hnz1102/timeleapcam/code/src/autofocus.rs

use log::info;
use esp_camera_rs::CameraSensor;
use std::{thread, time::Duration};

#[allow(dead_code)]
const OV5640_RESET : u16 = 0x3000;
const OV5640_CHIPID_HIGH : u16 = 0x300a;
const OV5640_CHIPID_LOW : u16 = 0x300b;
const OV5640_CMD_MAIN : u16 = 0x3022;
const OV5640_CMD_ACK : u16 = 0x3023;
const OV5640_CMD_PARA0 : u16 = 0x3024;
const OV5640_CMD_PARA1 : u16 = 0x3025;
const OV5640_CMD_PARA2 : u16 = 0x3026;
const OV5640_CMD_PARA3 : u16 = 0x3027;
const OV5640_CMD_PARA4 : u16 = 0x3028;
const OV5640_CMD_FW_STATUS : u16 = 0x3029;
const AF_TRIG_SINGLE_AUTO_FOCUS : u8 = 0x03;
const AF_GET_FOCUS_RESULT : u8 = 0x07;
#[allow(dead_code)]
const AF_RELEASE_FOCUS : u8 = 0x08;
const AF_RELAUNCH_ZONE_CONFIGURATION : u8 = 0x12;
const AF_LAUNCH_DEFAULT_ZONE : u8 = 0x80;
const FW_STATUS_S_FIRMWARE : u8 = 0x7F;
#[allow(dead_code)]
const FW_STATUS_S_STARTUP : u8 = 0x7E;
const FW_STATUS_S_IDLE : u8 = 0x70;
#[allow(dead_code)]
const FW_STATUS_S_FOCUSED : u8 = 0x10;
#[allow(dead_code)]
const FW_STATUS_S_ZONE_CONFIG : u8 = 0x16;
#[allow(dead_code)]
const FW_STATUS_S_FOCUSING : u8 = 0x00; //0x00 - 0X0F, 0x80 - 0X8F
const ALL_MASK : u8 = 0xFF;

pub struct AutoFocus<'a> {
    sensor: &'a CameraSensor<'a>,
	enable: bool,
}

impl<'a> AutoFocus<'a> {
    pub fn new(sensor: &'a CameraSensor) -> Self {
        Self { sensor: sensor, enable: false }
    }

    pub fn init(&mut self) {
        let pidh = self.sensor.get_reg(OV5640_CHIPID_HIGH, ALL_MASK);
        let pidl = self.sensor.get_reg(OV5640_CHIPID_LOW, ALL_MASK);
        info!("Autofocus PID: 0x{:x}{:x}", pidh, pidl);
		if pidh != 0x56 || pidl != 0x40 {
			info!("Autofocus not supported");
			return;
		}
		self.enable = true;
        self.sensor.set_reg(OV5640_RESET, ALL_MASK, 0x20).expect("Failed to reset the camera");
        for i in 0..AUTOFOCUS_CONFIG.len() {
            match self.sensor.set_reg((0x8000 + i) as u16, ALL_MASK, AUTOFOCUS_CONFIG[i]){
                Ok(_) => {},
                Err(e) => { info!("Failed to set register: {}", e); }
            }
        }
        let _ = self.sensor.set_reg(OV5640_CMD_MAIN, ALL_MASK, 0x00);
        let _ = self.sensor.set_reg(OV5640_CMD_ACK, ALL_MASK, 0x00);
        let _ = self.sensor.set_reg(OV5640_CMD_PARA0, ALL_MASK, 0x00);
        let _ = self.sensor.set_reg(OV5640_CMD_PARA1, ALL_MASK, 0x00);
        let _ = self.sensor.set_reg(OV5640_CMD_PARA2, ALL_MASK, 0x00);
        let _ = self.sensor.set_reg(OV5640_CMD_PARA3, ALL_MASK, 0x00);
        let _ = self.sensor.set_reg(OV5640_CMD_PARA4, ALL_MASK, 0x00);
        let _ = self.sensor.set_reg(OV5640_CMD_FW_STATUS, ALL_MASK, FW_STATUS_S_FIRMWARE);
        let _ = self.sensor.set_reg(OV5640_RESET, ALL_MASK, 0x00);

        info!("Waiting for autofocus to start...");
        loop {
            thread::sleep(Duration::from_millis(5));
			let status = self.sensor.get_reg(OV5640_CMD_FW_STATUS, ALL_MASK);
            if status == FW_STATUS_S_IDLE {
                break;
            }
        }
        info!("Autofocus initialized");
    }

	// if sensor resolution is changed, this function should be called
    pub fn autofocus_zoneconfig(&self) {
		if !self.enable {
			return;
		}
        let _ = self.sensor.set_reg(OV5640_CMD_ACK, ALL_MASK, 0x01);
        let _ = self.sensor.set_reg(OV5640_CMD_MAIN, ALL_MASK, AF_RELAUNCH_ZONE_CONFIGURATION);
        loop {
            thread::sleep(Duration::from_millis(5));
			let status = self.sensor.get_reg(OV5640_CMD_ACK, ALL_MASK);
			if status == 0x00 {
                break;
            }
        }
        let _ = self.sensor.set_reg(OV5640_CMD_ACK, ALL_MASK, 0x01);
        let _ = self.sensor.set_reg(OV5640_CMD_MAIN, ALL_MASK, AF_LAUNCH_DEFAULT_ZONE);
        loop {
            thread::sleep(Duration::from_millis(5));
			let status = self.sensor.get_reg(OV5640_CMD_ACK, ALL_MASK);
			if status == 0x00 {
                break;
            }
        }
        info!("AutoFocus Mode Enabled");
    }

	// autofocus trigger
	pub fn autofocus(&self) {
		if !self.enable {
			return;
		}
		info!("AutoFocus Triggered");
		let _ = self.sensor.set_reg(OV5640_CMD_ACK, ALL_MASK, 0x01);
		let _ = self.sensor.set_reg(OV5640_CMD_MAIN, ALL_MASK, AF_TRIG_SINGLE_AUTO_FOCUS);
		let mut count = 0;
		loop {
			thread::sleep(Duration::from_millis(10));
			let status = self.sensor.get_reg(OV5640_CMD_ACK, ALL_MASK);
			if status == 0x00 {
				info!("AutoFocus Done");
                break;
            }
			count += 1;
			if count > 1000 {
				info!("AutoFocus Timeout");
				break;
			}
		}
	}

	pub fn get_focus_result(&self) -> u8 {
		if !self.enable {
			return 0xFF;
		}
		let _ = self.sensor.set_reg(OV5640_CMD_ACK, ALL_MASK, 0x01);
		let _ = self.sensor.set_reg(OV5640_CMD_MAIN, ALL_MASK, AF_GET_FOCUS_RESULT);
		let mut count = 0;
		loop {
			thread::sleep(Duration::from_millis(10));
			count += 1;
			let status = self.sensor.get_reg(OV5640_CMD_ACK, ALL_MASK);
			if status == 0x00 {
				let result = self.sensor.get_reg(OV5640_CMD_PARA0, ALL_MASK);
				let _ = self.sensor.get_reg(OV5640_CMD_PARA1, ALL_MASK);
				let _ = self.sensor.get_reg(OV5640_CMD_PARA2, ALL_MASK);
				let _ = self.sensor.get_reg(OV5640_CMD_PARA3, ALL_MASK);
				let _ = self.sensor.get_reg(OV5640_CMD_PARA4, ALL_MASK);
				if result == 0x00 {
					info!("AutoFocus Focused");
				} else {
					info!("AutoFocus Not Focused");
				}
				return result;	// zero is focused
			}
			if count > 2000 {
				info!("AutoFocus Timeout");
				return 0xFF;
			}
		}
	}

	#[allow(dead_code)]
	pub fn release_focus(&self) {
		if !self.enable {
			return;
		}
		let _ = self.sensor.set_reg(OV5640_CMD_ACK, ALL_MASK, 0x01);
		let _ = self.sensor.set_reg(OV5640_CMD_MAIN, ALL_MASK, AF_RELEASE_FOCUS);
		loop {
			thread::sleep(Duration::from_millis(5));
			let status = self.sensor.get_reg(OV5640_CMD_ACK, ALL_MASK);
			if status == 0x00 {
				break;
			}
		}
		info!("AutoFocus Released");
	}

	#[allow(dead_code)]
    pub fn get_focus_status(&self) -> u8 {
		if !self.enable {
			return 0xFF;
		}
        self.sensor.get_reg(OV5640_CMD_FW_STATUS, ALL_MASK)
    }
}

const AUTOFOCUS_CONFIG: &[u8] = &[
	0x02, 0x0f, 0xd6, 0x02, 0x0a, 0x39, 0xc2, 0x01, 0x22, 0x22, 0x00, 0x02, 0x0f, 0xb2, 0xe5, 0x1f, //0x8000,
	0x70, 0x72, 0xf5, 0x1e, 0xd2, 0x35, 0xff, 0xef, 0x25, 0xe0, 0x24, 0x4e, 0xf8, 0xe4, 0xf6, 0x08, //0x8010,
	0xf6, 0x0f, 0xbf, 0x34, 0xf2, 0x90, 0x0e, 0x93, 0xe4, 0x93, 0xff, 0xe5, 0x4b, 0xc3, 0x9f, 0x50, //0x8020,
	0x04, 0x7f, 0x05, 0x80, 0x02, 0x7f, 0xfb, 0x78, 0xbd, 0xa6, 0x07, 0x12, 0x0f, 0x04, 0x40, 0x04, //0x8030,
	0x7f, 0x03, 0x80, 0x02, 0x7f, 0x30, 0x78, 0xbc, 0xa6, 0x07, 0xe6, 0x18, 0xf6, 0x08, 0xe6, 0x78, //0x8040,
	0xb9, 0xf6, 0x78, 0xbc, 0xe6, 0x78, 0xba, 0xf6, 0x78, 0xbf, 0x76, 0x33, 0xe4, 0x08, 0xf6, 0x78, //0x8050,
	0xb8, 0x76, 0x01, 0x75, 0x4a, 0x02, 0x78, 0xb6, 0xf6, 0x08, 0xf6, 0x74, 0xff, 0x78, 0xc1, 0xf6, //0x8060,
	0x08, 0xf6, 0x75, 0x1f, 0x01, 0x78, 0xbc, 0xe6, 0x75, 0xf0, 0x05, 0xa4, 0xf5, 0x4b, 0x12, 0x0a, //0x8070,
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
	0xc3, 0x12, 0x0e, 0xe9, 0x40, 0x02, 0xd2, 0x37, 0x75, 0x1f, 0x05, 0x22, 0x30, 0x01, 0x03, 0x02, //0x8260,
	0x04, 0xc0, 0x30, 0x02, 0x03, 0x02, 0x04, 0xc0, 0x90, 0x51, 0xa5, 0xe0, 0x78, 0x93, 0xf6, 0xa3, //0x8270,
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
];
