hnz1102/timeleapcam/code/src/imagefiles.rs

use anyhow;
use log::info;
use std::fs;
use std::path::Path;
use std::io::{Write, Read, Seek};
use std::sync::{Arc, Mutex};
use std::thread;
use std::time::Duration;

const IMAGE_HEADER_SIZE: usize = 8;
const MAX_QUEUE_SIZE: usize = 4 * 1024 * 1024;
const MAX_TEMP_BUF_SIZE: usize = 8 * 1024;

#[derive(Debug, PartialEq, Clone)]
pub enum OpenMode {
    Read,
    Write,
    Append,
}

#[derive(Debug, PartialEq, Clone)]
pub enum WriteThreadStatus {
    NotStarted,
    Running,
    Stopped,
}

pub struct WriteImageQueue {
    buffer: Vec<Box<[u8]>>,
    data_size: usize,
    thread_status: WriteThreadStatus,
    write_done: bool,
    images: u32,
    queue_len: usize,
}

pub struct WriteThread {
    file_path: String,
    open_mode: OpenMode,
    direct_write_mode: bool,
    image_file: Option<ImageFiles>,
    buffer_is_full: bool,
    drop_frames: u32,
    write_image_queue: Arc<Mutex<WriteImageQueue>>,
}

impl WriteThread {
    pub fn new(filepath: String, open_mode: OpenMode, direct_write_mode: bool) -> WriteThread {
        WriteThread {
            file_path: filepath.clone(),
            write_image_queue: Arc::new(Mutex::new(WriteImageQueue {
                buffer: Vec::new(),
                data_size: 0,
                thread_status: WriteThreadStatus::NotStarted,
                write_done: false,
                images: 0,
                queue_len: 0,
            })),
            open_mode: open_mode.clone(),
            direct_write_mode: direct_write_mode,
            image_file: Option::None,
            buffer_is_full: false,
            drop_frames: 0,
        }
    }

    pub fn start(&mut self) {
        if self.direct_write_mode {
            let image_file = match ImageFiles::new(&self.file_path, self.open_mode.clone()) {
                Ok(img) => img,
                Err(e) => {
                    info!("Error: {:?}", e);
                    return;
                }
            };
            self.image_file = Some(image_file);
            return; // Direct write mode does not need a thread
        }
        let write_image_queue = self.write_image_queue.clone();
        let file_path = self.file_path.clone();
        let open_mode = self.open_mode.clone();
        let _th = std::thread::spawn(move || {
            info!("WriteThread start");
            let mut image_file = match ImageFiles::new(file_path, open_mode) {
                Ok(img) => img,
                Err(e) => {
                    info!("Error: {:?}", e);
                    return;
                }
            };
            let mut write_image_time : u128 = 0;

            let mut data_count = 0;
            let start_time = std::time::SystemTime::now();
            loop {
                let mut wiqlk = write_image_queue.lock().unwrap();
                wiqlk.thread_status = WriteThreadStatus::Running;
                if wiqlk.buffer.len() > 0 {
                    let data = wiqlk.buffer.remove(0);
                    let data_size = data.len();
                    wiqlk.data_size += data_size;
                    wiqlk.queue_len -= data_size;
                    // let remaining = wiqlk.buffer.len();
                    drop(wiqlk);
                    let write_time = std::time::SystemTime::now();
                    let _ = image_file.write_image(&data); 
                    let elapsed_time = write_time.elapsed().unwrap().as_micros();
                    write_image_time += elapsed_time;
                    data_count += 1;
                    continue;
                } else if wiqlk.write_done {
                    break;
                }
                else {
                    drop(wiqlk);
                }
                thread::sleep(Duration::from_millis(10));
            }
            let _ = image_file.write_image_end();
            let elapsed_time = start_time.elapsed().unwrap().as_millis();
            let mut qlk = write_image_queue.lock().unwrap();
            qlk.images = image_file.get_nof_images();
            info!("WriteThread Write images: {} time: {:?}ms {:.2}MB/s Ave: {:.2}ms",
                qlk.images, 
                elapsed_time, 
                qlk.data_size as f32 / elapsed_time as f32 / 1024.0,
                write_image_time as f32 / data_count as f32 / 1000.0);
            qlk.thread_status = WriteThreadStatus::Stopped;
            info!("WriteThread end");
        });
    }

    pub fn push_data(&mut self, data: &[u8]) {
        let mut wiqlk = self.write_image_queue.lock().unwrap();
        if self.direct_write_mode {
            let _ = self.image_file.as_mut().unwrap().write_image(&data);
            return;
        }
        // delayed write, check the queue size
        if wiqlk.queue_len + data.len() > MAX_QUEUE_SIZE {
            self.drop_frames += 1;
            if !self.buffer_is_full {
                info!("WriteThread Queue is full: {:.2}KB {} Bufs.", wiqlk.queue_len / 1024, wiqlk.buffer.len());
                self.buffer_is_full = true;
            }
            return;
        }
        if self.buffer_is_full {
            if data.len() == 0 {
                self.buffer_is_full = false;
            }
        }
        wiqlk.queue_len += data.len();
        let binding = data.to_vec().into_boxed_slice();
        wiqlk.buffer.push(binding);
    }

    pub fn stop(&mut self) {
        let mut wiqlk = self.write_image_queue.lock().unwrap();
        if self.direct_write_mode {
            let _ = self.image_file.as_mut().unwrap().write_image_end();
            self.image_file.as_mut().unwrap().flush();
            wiqlk.images = self.image_file.as_ref().unwrap().get_nof_images();
        }
        wiqlk.write_done = true;
        info!("Drop Frames: {}", self.drop_frames);
    }

    pub fn get_nof_images(&self) -> u32 {
        let wiqlk = self.write_image_queue.lock().unwrap();
        wiqlk.images
    }
    
    pub fn wait_thread(&self) {
        loop {
            let wiqlk = self.write_image_queue.lock().unwrap();
            if self.direct_write_mode {
                break;
            }
            if wiqlk.thread_status == WriteThreadStatus::Stopped {
                break;
            }
            drop(wiqlk);
            thread::sleep(Duration::from_millis(10));
        }
    }
}

pub struct ImageFiles {
    file: fs::File,
    nimages: u32, 
    read_pos: u64,
    write_pos: u64,
    total_size: u64,
    total_copy_time: u128,
    total_write_time: u128,
    write_count: u32,
    last_image_pos: u64,
}

const FILE_HEADER_SIZE: usize = 24;
const FILE_HEADER: [u8; FILE_HEADER_SIZE] = ['T' as u8, 'C' as u8, 'A' as u8, 'M' as u8,
                               0, 0, 0, 0,                  // Total number of images
                               0, 0, 0, 0, 0, 0, 0, 0,      // Total size of images
                               0, 0, 0, 0, 0, 0, 0, 0,      // Last Image Offset
                               ];

impl ImageFiles {
    pub fn new(directory: impl AsRef<Path>, mode: OpenMode) -> Result<ImageFiles, anyhow::Error> {
        let file = match mode {
            // Open the file for writing only
            OpenMode::Write => fs::OpenOptions::new()
                .read(true)
                .write(true)
                .create(true)
                .open(directory.as_ref()),
            OpenMode::Append => fs::OpenOptions::new()
                .read(true)
                .write(true)
                .create(true)
                .open(directory.as_ref()),
            OpenMode::Read => fs::OpenOptions::new()
                .read(true)
                .create(false)
                .open(directory.as_ref()), 
        };
        match file {
            Ok(mut file) => {
                let mut header : [u8; FILE_HEADER_SIZE] = [0; FILE_HEADER_SIZE];
                let _ = file.read(&mut header);
                let total_size : u64;
                let mut nimages : u32 = 0;
                let mut last_image_pos : u64 = 0;
                if mode == OpenMode::Write {
                    // renew the file header
                    let _ = file.seek(std::io::SeekFrom::Start(0));
                    let _ = file.write(&FILE_HEADER);
                    total_size = 0;
                }
                else {
                    let mut renew_header = false;
                    for i in 0..4 {
                        if header[i] != FILE_HEADER[i] {
                            if mode == OpenMode::Read {
                                info!("Invalid file header: {:?}", header);
                                return Err(anyhow::Error::msg("Invalid file header"));
                            }
                            info!("Invalid file header: {:?} => Rewrite Header", header);
                            let _ = file.seek(std::io::SeekFrom::Start(0));
                            let _ = file.write(&FILE_HEADER);
                            renew_header = true;
                            break;
                        }
                    }
                    total_size = match renew_header {
                        true => 0,
                        false => {
                            let size = 
                                (header[8] as u64) +
                                ((header[9] as u64) << 8) +
                                ((header[10] as u64) << 16) +
                                ((header[11] as u64) << 24) +
                                ((header[12] as u64) << 32) +
                                ((header[13] as u64) << 40) +
                                ((header[14] as u64) << 48) +
                                ((header[15] as u64) << 56);
                            size
                        },
                    };
                    nimages = match renew_header {
                        true => 0,
                        false => {
                            let n = 
                                (header[4] as u32) +
                                ((header[5] as u32) << 8) +
                                ((header[6] as u32) << 16) +
                                ((header[7] as u32) << 24);
                            n
                        },
                    };
                    last_image_pos = match renew_header {
                        true => 0,
                        false => {
                            let pos = 
                                (header[16] as u64) +
                                ((header[17] as u64) << 8) +
                                ((header[18] as u64) << 16) +
                                ((header[19] as u64) << 24) +
                                ((header[20] as u64) << 32) +
                                ((header[21] as u64) << 40) +
                                ((header[22] as u64) << 48) +
                                ((header[23] as u64) << 56);
                            pos
                        },
                    };
                }
                let read_pos = FILE_HEADER.len() as u64;
                let write_pos = match mode {
                    OpenMode::Append => total_size + read_pos,
                    _ => read_pos,
                };
                Ok(ImageFiles {
                    file: file,
                    nimages: nimages,
                    read_pos: read_pos,
                    write_pos: write_pos,
                    total_size: total_size,
                    total_copy_time: 0,
                    total_write_time: 0,
                    write_count: 0,
                    last_image_pos: last_image_pos,
                })
            }
            Err(e) => {
                info!("Failed to open file: {:?}", e);
                Err(anyhow::Error::msg("Failed to open file"))
            }
        }
    }

    #[allow(dead_code)]
    pub fn read(&mut self, buffer: &mut [u8]) -> usize {
        if self.read_pos >= self.total_size + FILE_HEADER.len() as u64 {
            return 0;
        }
        self.file.seek(std::io::SeekFrom::Start(self.read_pos)).unwrap();
        let bytes_read = self.file.read(buffer).unwrap();
        self.read_pos += bytes_read as u64;
        bytes_read
    }

    #[allow(dead_code)]
    pub fn write(&mut self, buffer: &[u8]) {
        self.file.seek(std::io::SeekFrom::Start(self.write_pos)).unwrap();
        self.file.write(buffer).unwrap();
        self.write_pos += buffer.len() as u64;
    }

    #[allow(dead_code)]
    pub fn seek(&mut self, pos: u64) {
        self.read_pos = pos;
    }

    #[allow(dead_code)]
    pub fn flush(&mut self) {
        self.file.flush().unwrap();
    }

    pub fn write_image(&mut self, buffer: &[u8]) -> Result<(), anyhow::Error> {
        let size = buffer.len();
        let header = [
            'D' as u8,
            'A' as u8,
            'T' as u8,
            'A' as u8,
            (size & 0xFF) as u8,
            ((size >> 8) & 0xFF) as u8,
            ((size >> 16) & 0xFF) as u8,
            ((size >> 24) & 0xFF) as u8,
        ];
        let save_write_pos = self.write_pos;
        self.file.seek(std::io::SeekFrom::Start(self.write_pos))?;
        self.file.write(&header)?;
        // Write the image data
        // To copy the buffer to the temporary buffer, it is faster than writing directly.
        // When data is written to the eMMC, the data read from the SPIRAM is slow.
        // Workaround: Copy the data to the temporary buffer and write it to the eMMC. 
        let mut cp = 0;
        let mut data_size = size;
        let mut tmp_buf : [u8; MAX_TEMP_BUF_SIZE] = [0; MAX_TEMP_BUF_SIZE];
        loop {
            let write_size: usize;
            if data_size > MAX_TEMP_BUF_SIZE {
                write_size = MAX_TEMP_BUF_SIZE;
                let copy_start = std::time::Instant::now();
                tmp_buf.copy_from_slice(&buffer[cp..(cp+write_size)]);
                self.total_copy_time += copy_start.elapsed().as_micros();
                let write_start = std::time::Instant::now();
                self.file.write_all(&tmp_buf)?;
                self.total_write_time += write_start.elapsed().as_micros();
            }
            else {
                write_size = data_size;
                let copy_start = std::time::Instant::now();
                let (l, _) = tmp_buf.split_at_mut(write_size);
                l.copy_from_slice(&buffer[cp..(cp+write_size)]);
                self.total_copy_time += copy_start.elapsed().as_micros();
                let write_start = std::time::Instant::now();
                self.file.write_all(&l)?;
                self.total_write_time += write_start.elapsed().as_micros();
            }
            // info!("WriteThread data_size: {} Write size: {:?}bytes {}..{}", data_size, write_size, cp, cp+write_size);
            data_size -= write_size;
            cp += write_size;
            if data_size == 0 {
                break;
            }
        }
        // let write_start = std::time::Instant::now();
        // self.file.write(&buffer)?;
        // self.total_write_time += write_start.elapsed().as_micros();
        self.write_count += 1;
        self.write_pos += (size + IMAGE_HEADER_SIZE) as u64;
        self.total_size += (size + IMAGE_HEADER_SIZE) as u64;
        self.last_image_pos = save_write_pos;
        self.nimages += 1;
        Ok(())
    }

    pub fn write_image_end(&mut self) -> Result<(), anyhow::Error> {
        let header = [
            'E' as u8,
            'N' as u8,
            'D' as u8,
            0 as u8,
            0 as u8,
            0 as u8,
            0 as u8,
            0 as u8,
        ];
        self.file.seek(std::io::SeekFrom::Start(self.write_pos))?;
        self.file.write(&header)?;
        self.write_pos += IMAGE_HEADER_SIZE as u64;
        // Update write position in the file header
        self.file.seek(std::io::SeekFrom::Start(4))?;
        let file_nimages_header : [u8; 4 ] = [
            (self.nimages & 0xFF) as u8,
            ((self.nimages >> 8) & 0xFF) as u8,
            ((self.nimages >> 16) & 0xFF) as u8,
            ((self.nimages >> 24) & 0xFF) as u8,
        ];
        self.file.write(&file_nimages_header)?;
        let file_size_header : [u8; 8 ] = [
            (self.total_size & 0xFF) as u8,
            ((self.total_size >> 8) & 0xFF) as u8,
            ((self.total_size >> 16) & 0xFF) as u8,
            ((self.total_size >> 24) & 0xFF) as u8,
            ((self.total_size >> 32) & 0xFF) as u8,
            ((self.total_size >> 40) & 0xFF) as u8,
            ((self.total_size >> 48) & 0xFF) as u8,
            ((self.total_size >> 56) & 0xFF) as u8,
        ]; 
        self.file.write(&file_size_header)?;
        let file_last_image_pos_header : [u8; 8 ] = [
            (self.last_image_pos & 0xFF) as u8,
            ((self.last_image_pos >> 8) & 0xFF) as u8,
            ((self.last_image_pos >> 16) & 0xFF) as u8,
            ((self.last_image_pos >> 24) & 0xFF) as u8,
            ((self.last_image_pos >> 32) & 0xFF) as u8,
            ((self.last_image_pos >> 40) & 0xFF) as u8,
            ((self.last_image_pos >> 48) & 0xFF) as u8,
            ((self.last_image_pos >> 56) & 0xFF) as u8,
        ];
        self.file.write(&file_last_image_pos_header)?;
        info!("WriteThread Ave Copy time: {:.2}ms Ave Write time: {:.2}ms", 
            self.total_copy_time as f32 / self.write_count as f32 / 1000.0, 
            self.total_write_time as f32 / self.write_count as f32 / 1000.0);
        Ok(())
    }

    pub fn get_image_size(&mut self) -> usize {
        if self.read_pos >= self.total_size + FILE_HEADER.len() as u64 {
            return 0;
        }
        let _ = self.file.seek(std::io::SeekFrom::Start(self.read_pos));
        let mut header : [u8; IMAGE_HEADER_SIZE] = [0; IMAGE_HEADER_SIZE];
        let hsize = match self.file.read(&mut header){
            Ok(hsize) => hsize,
            Err(e) => {
                info!("Failed to read header: {:?}", e);
                return 0;
            }
        };

        if hsize != IMAGE_HEADER_SIZE {
            info!("Failed to read header size: {:?}byte", hsize);
            return 0;
        }
        // Check if the header is valid
        if header[0] != 'D' as u8 ||
           header[1] != 'A' as u8 ||
           header[2] != 'T' as u8 ||
           header[3] != 'A' as u8 {
                if  header[0] != 'E' as u8 ||
                    header[1] != 'N' as u8 ||
                    header[2] != 'D' as u8 ||
                    header[3] != 0 as u8 {
                        info!("Invalid Header {:?}", header);
                }
                return 0;
        }
        // Get the size of the image
        let size =  (header[4] as usize) +
                    ((header[5] as usize) << 8) +
                    ((header[6] as usize) << 16) +
                    ((header[7] as usize) << 24);
        size
    }

    pub fn read_image(&mut self) -> Result<Vec<u8>, anyhow::Error> {
        let size = self.get_image_size();
        if size == 0 {
            return Err(anyhow::Error::msg("Failed to get image size at Read"));
        }
        let mut buffer = vec![0; size];
        let _ = self.file.seek(std::io::SeekFrom::Start(self.read_pos + IMAGE_HEADER_SIZE as u64));
        let bytes_read = match self.file.read(&mut buffer[0..size]){
            Ok(bytes_read) => bytes_read,
            Err(e) => {
                info!("Failed to read image: {:?}", e);
                return Err(anyhow::Error::msg("Failed to read image"));
            }
        };
        self.read_pos += (bytes_read + IMAGE_HEADER_SIZE) as u64;
        Ok(buffer)
    }

    pub fn seek_image(&mut self, from_frame: u32) -> Result<(), anyhow::Error> {
        if from_frame == self.nimages - 1 {
            self.read_pos = self.last_image_pos;
            return Ok(());
        }
        for _ in 0..from_frame {
            let size = self.get_image_size();
            if size == 0 {
                return Err(anyhow::Error::msg("Failed to get image size at Seek"));
            }
            self.read_pos += (size + IMAGE_HEADER_SIZE) as u64;
        }
        Ok(())
    }

    pub fn get_nof_images(&self) -> u32 {
        self.nimages
    }
}

// Read the Capture file
#[allow(dead_code)]
pub fn read_file(filepath: &Path) -> Vec<u8> {
    let file = fs::File::open(filepath);
    match file {
        Ok(mut file) => {
            let mut buffer = Vec::new();
            match file.read_to_end(&mut buffer) {
                Ok(_) => {
                    info!("File read successfully {:?} {:?} bytes", filepath, buffer.len());
                    buffer
                }
                Err(e) => {
                    info!("Failed to read file: {:?}", e);
                    Vec::new()
                }
            }
        }
        Err(e) => {
            info!("Failed to open file: {:?}", e);
            Vec::new()
        }
    }
}

// Write the Capture file
#[allow(dead_code)]
pub fn write_file(file: &Path, data: &[u8]) {
    // info!("Writing file: {:?}", file);
    let file = fs::File::create(file);
    match file {
        Ok(mut file) => {
            match file.write(data) {
                Ok(_) => {
                    // info!("File written successfully");
                }
                Err(e) => {
                    info!("Failed to write file: {:?}", e);
                }
            }
            // file.flush().unwrap();
        }
        Err(e) => {
            info!("Failed to create file: {:?}", e);
        }
    }
}

// List files in the directory
#[allow(dead_code)]
pub fn list_files(directory: &Path ) {
    // Create a file
    let file = fs::read_dir(directory);
    match file {
        Ok(file) => {
            for entry in file {
                let entry = entry.unwrap();
                info!("{:?} Len: {:?}", entry.path().display(), entry.metadata().unwrap().len());
            }        
        }
        Err(e) => {
            info!("Failed to open file: {:?}", e);
        }
    }
}

// Delete the Capture file
#[allow(dead_code)]
pub fn delete_file(file: &Path) {
    let result = fs::remove_file(file);
    match result {
        Ok(_) => {
            info!("File deleted successfully");
        }
        Err(e) => {
            info!("Failed to delete file: {:?}", e);
        }
    }
}

// Delete all files in the directory
#[allow(dead_code)]
pub fn delete_all_files(directory: &Path) {
    let result = fs::remove_dir_all(directory);
    match result {
        Ok(_) => {
            info!("Files deleted successfully");
        }
        Err(e) => {
            info!("Failed to delete files: {:?}", e);
        }
    }
}
